grodansparadis/can4vscp_power_injector/eagle_big/Gerbers/power_injector_rev_c_gbo_small.png

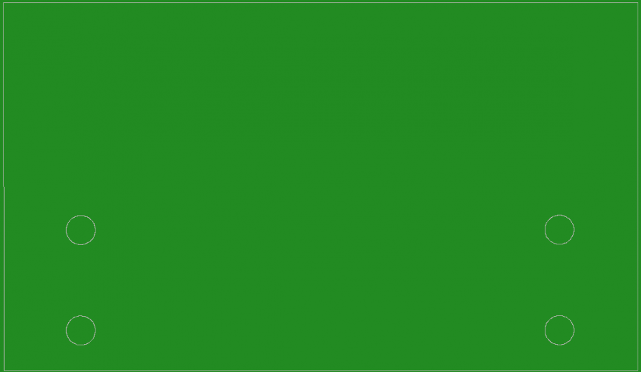
eagle_big/Gerbers/power_injector_rev_c_gbo_small.png
