grodansparadis/can4vscp_power_injector/eagle_big/power_injector_big_rev_c_sch.png

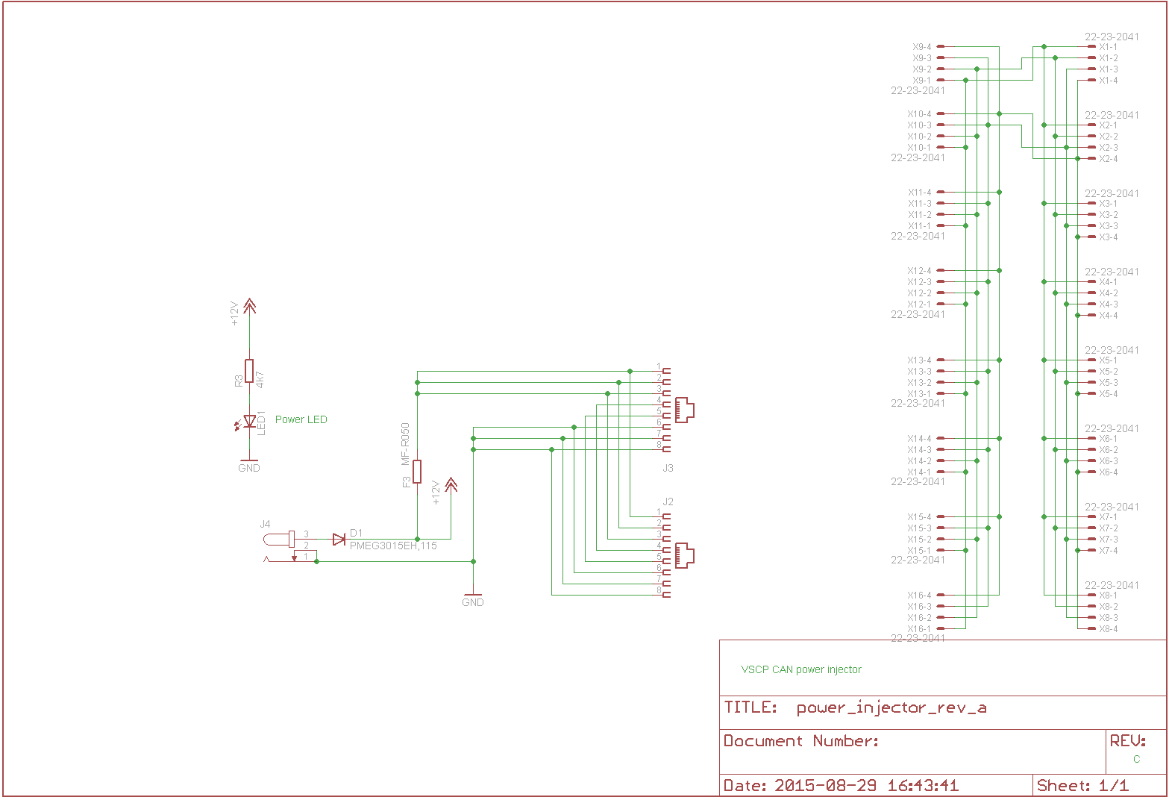
eagle_big/power_injector_big_rev_c_sch.png
