grodansparadis/can4vscp_power_injector/eagle_mini/power_injector_mini_rev_b_sch.png

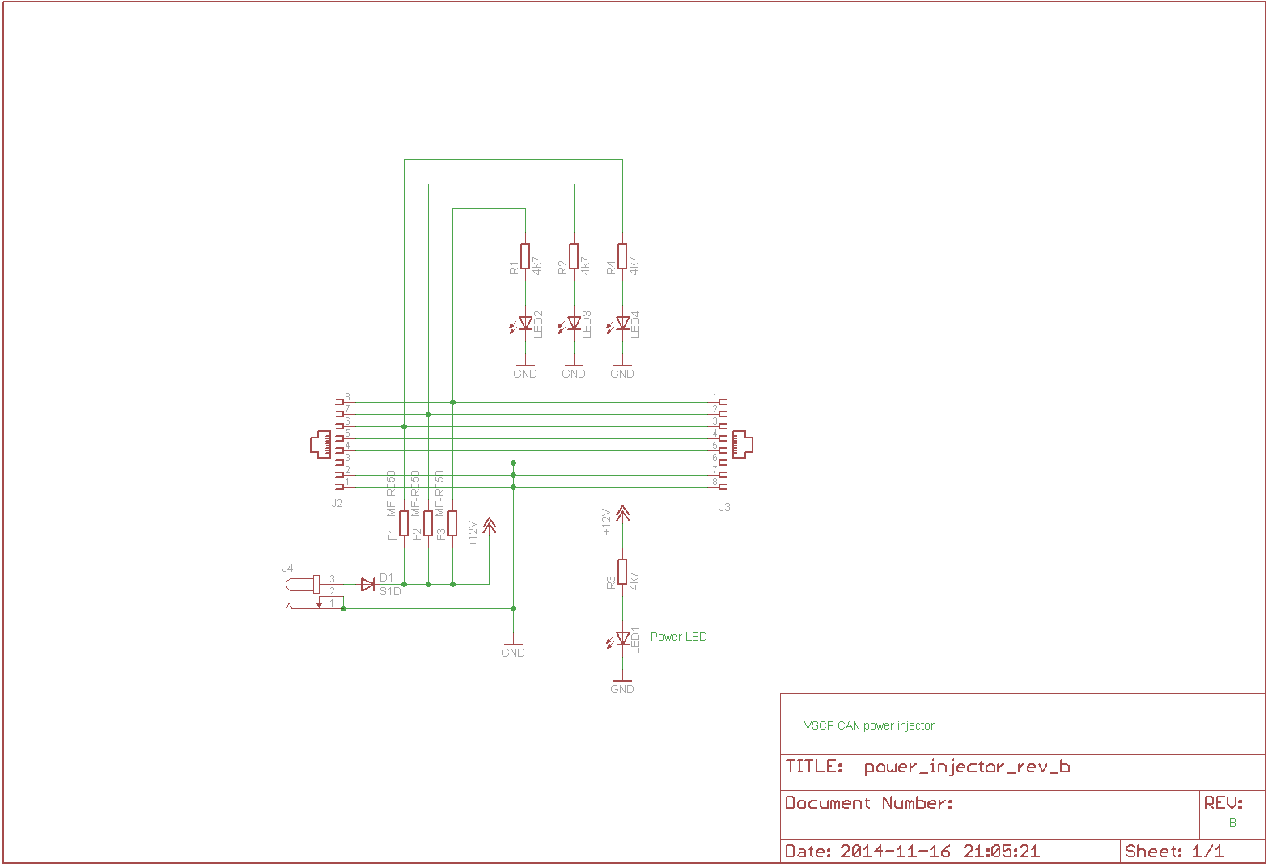
eagle_mini/power_injector_mini_rev_b_sch.png
